smillier/BeerTapRoundDisplay/Case/image.JPG

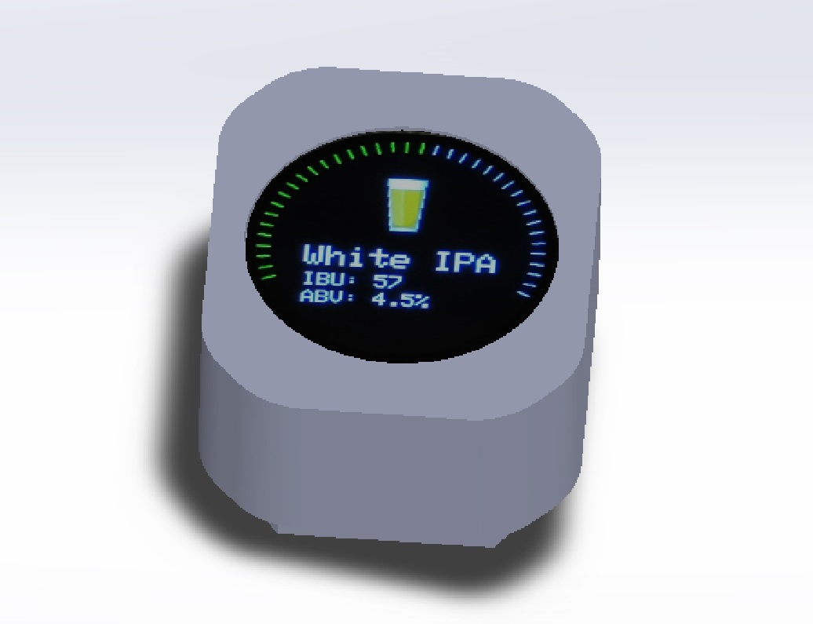
Case/image.JPG
