smillier/BeerTapRoundDisplay/doc/IMG_20211112_064714.jpg

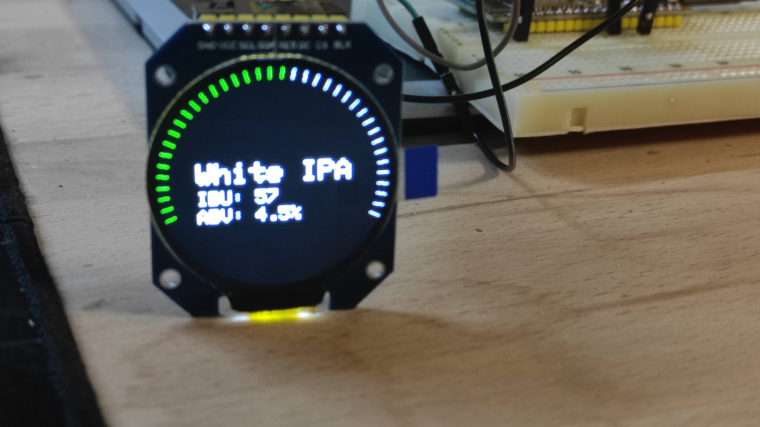
doc/IMG_20211112_064714.jpg
