smillier/BeerTapRoundDisplay/doc/IMG_20220213_194237.jpg

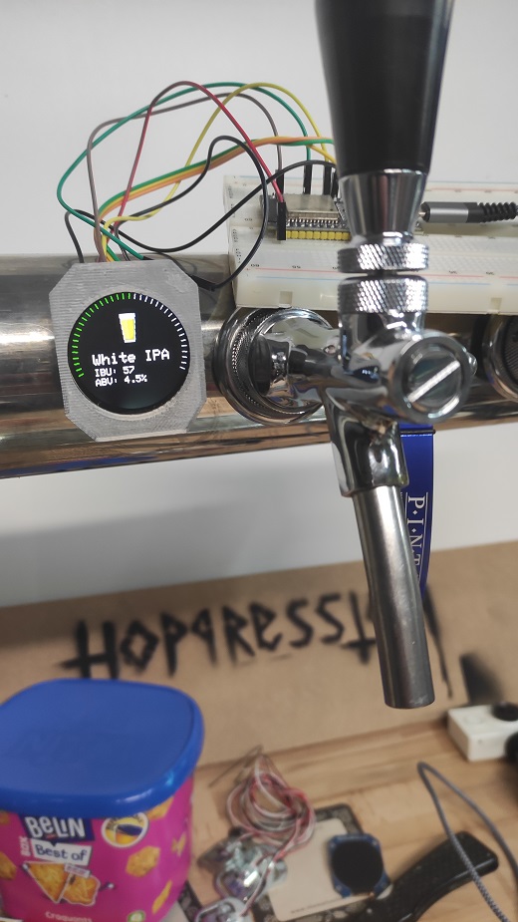
doc/IMG_20220213_194237.jpg
