smillier/BeerTapRoundDisplay/doc/IMG_20220216_224940.jpg

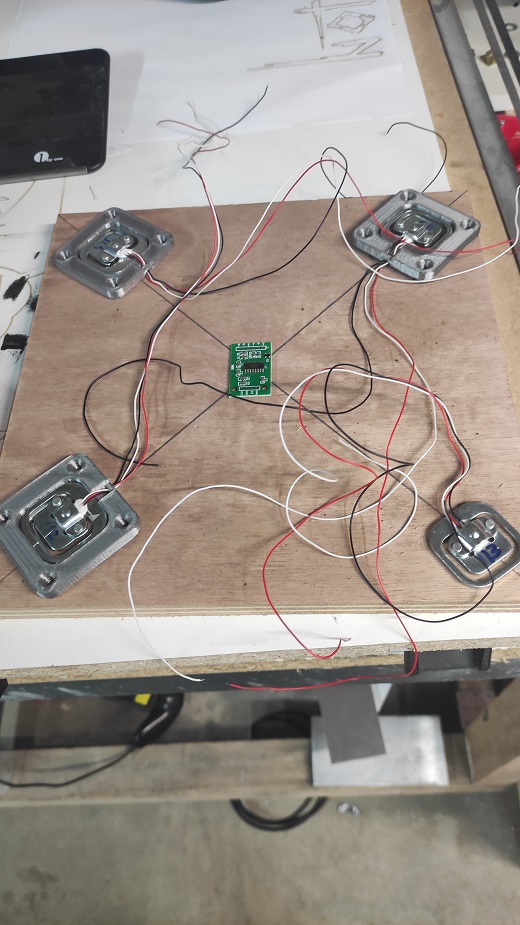
doc/IMG_20220216_224940.jpg
