smillier/BeerTapRoundDisplay/doc/IMG_20220629_192002.jpg

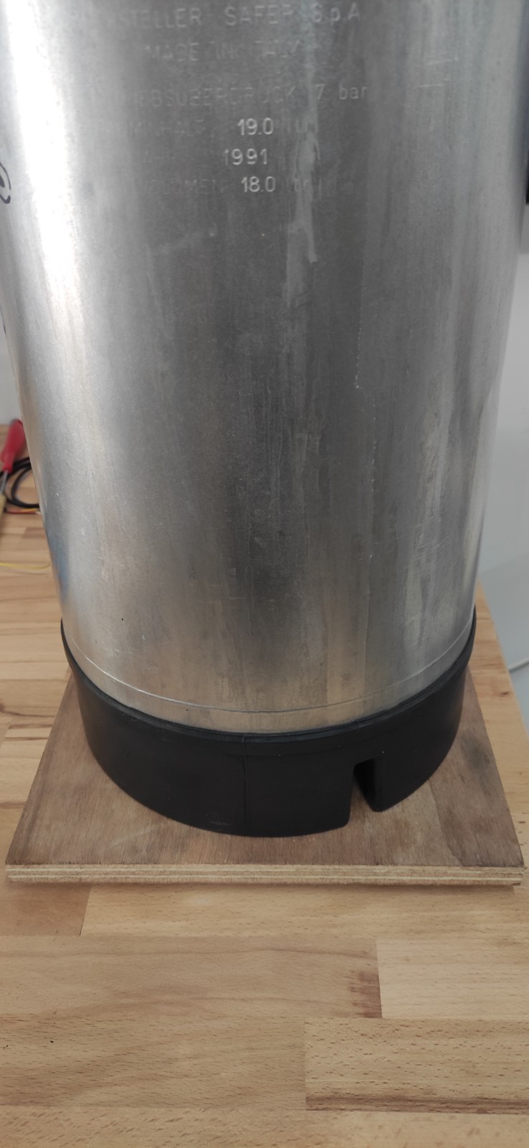
doc/IMG_20220629_192002.jpg
