smillier/BeerTapRoundDisplay/doc/IMG_20220629_192141.jpg

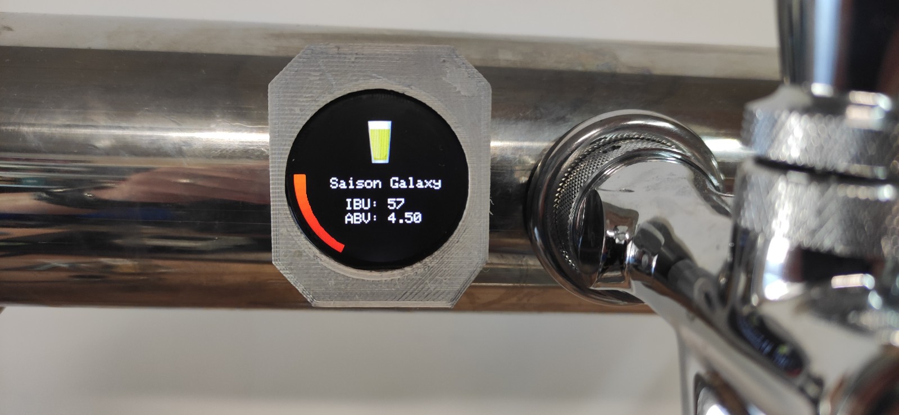
doc/IMG_20220629_192141.jpg
