smillier/BeerTapRoundDisplay/doc/ModuleDimensions.JPG

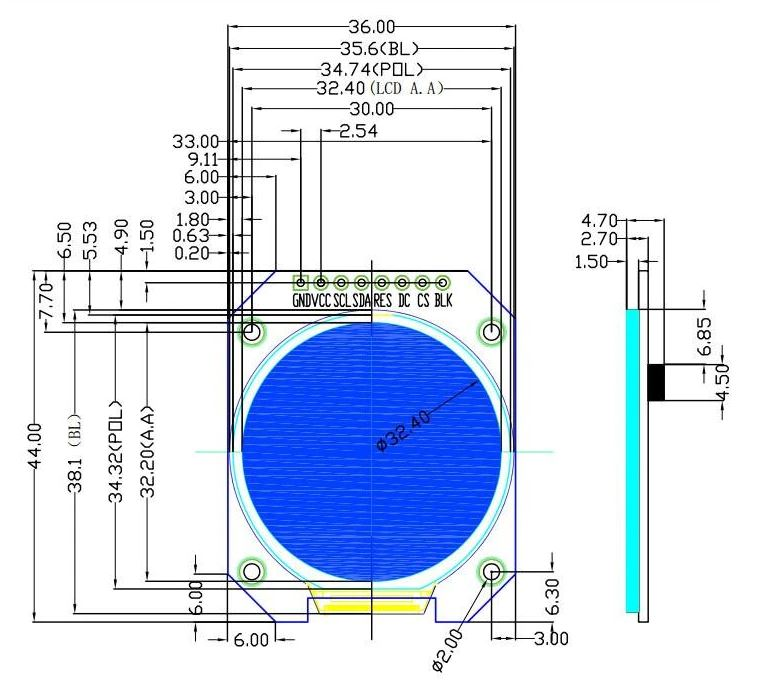
doc/ModuleDimensions.JPG
