smillier/BeerTapRoundDisplay/doc/NSRM12.png

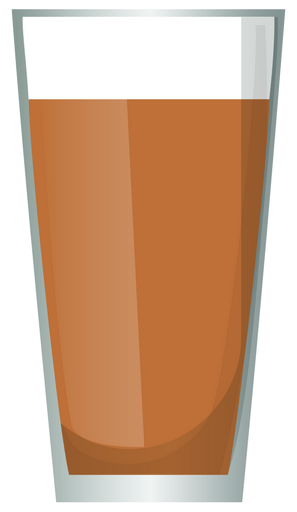
doc/NSRM12.png
