smillier/BeerTapRoundDisplay/src/setup.cpp

#include "setup.h"
#include "FS.h"
#include <SPIFFS.h>
#include <WiFi.h>

#include <AsyncTCP.h>
#include <ESPAsyncWebServer.h>
#include <AsyncElegantOTA.h>
#define _ESPASYNC_WIFIMGR_LOGLEVEL_    3
#include <WiFiClient.h>
#include <ESPmDNS.h>
#include <ArduinoOTA.h>
#include <ESPAsync_WiFiManager.h> 
#include "weightmeasure.h"
#include "display.h"
AsyncWebServer server(80);
#include "config.h"
#include "Preferences.h"

//Preferences preference;

void initialize()
{
  Serial.println("Init display");

  
 //AsyncWebServer webServer(80);
#if !( USING_ESP32_S2 || USING_ESP32_C3 )
DNSServer dnsServer;
#endif
//const char *ssid = "";
//const char *password = "";

  Serial.begin(115200);
  Serial.println("\n");
  Serial.println("Connexion etablie!");
  Serial.print("Adresse IP: ");
  Serial.println(WiFi.localIP());
  //mDNS Responder
  // Set up mDNS responder:
    // - first argument is the domain name, in this example
    //   the fully-qualified domain name is "esp32.local"
    // - second argument is the IP address to advertise
    //   we send our IP address on the WiFi network
    if (!MDNS.begin("BeerTapDisplay.local")) {
        Serial.println("Error setting up MDNS responder!");
        while(1) {
            delay(1000);
        }
    }
    Serial.println("mDNS responder started");

    Serial.println("TCP server started");

    // Add service to MDNS-SD
    MDNS.addService("http", "tcp", 80);
    //----------------------------------------------------OTA
  Serial.println("Starting OTA...");
  
    #if ( USING_ESP32_S2 || USING_ESP32_C3 )
  ESPAsync_WiFiManager ESPAsync_wifiManager(&server, NULL, "Bottle_Filler_Autoconnect");
#else
  ESPAsync_WiFiManager ESPAsync_wifiManager(&server, &dnsServer, "TapDisplay");
#endif  
  //ESPAsync_wifiManager.resetSettings();   //reset saved settings
  ESPAsync_wifiManager.setAPStaticIPConfig(IPAddress(192,168,4,1), IPAddress(192,168,4,1), IPAddress(255,255,255,0));
  ESPAsync_wifiManager.autoConnect("TapDisplay_AP");
  if (WiFi.status() == WL_CONNECTED) { Serial.print(F("Connected. Local IP: ")); Serial.println(WiFi.localIP()); }
  else { Serial.println(ESPAsync_wifiManager.getStatus(WiFi.status())); }
 
 ArduinoOTA
    .onStart([]() {
      String type;
      if (ArduinoOTA.getCommand() == U_FLASH)
        type = "sketch";
      else // U_SPIFFS
        type = "filesystem";

      // NOTE: if updating SPIFFS this would be the place to unmount SPIFFS using SPIFFS.end()
      Serial.println("Start updating " + type);
    })
    .onEnd([]() {
      Serial.println("\nEnd");
    })
    .onProgress([](unsigned int progress, unsigned int total) {
      Serial.printf("Progress: %u%%\r", (progress / (total / 100)));
    })
    .onError([](ota_error_t error) {
      Serial.printf("Error[%u]: ", error);
      if (error == OTA_AUTH_ERROR) Serial.println("Auth Failed");
      else if (error == OTA_BEGIN_ERROR) Serial.println("Begin Failed");
      else if (error == OTA_CONNECT_ERROR) Serial.println("Connect Failed");
      else if (error == OTA_RECEIVE_ERROR) Serial.println("Receive Failed");
      else if (error == OTA_END_ERROR) Serial.println("End Failed");
    });
    
    ArduinoOTA.begin();

    AsyncElegantOTA.begin(&server);    // Start ElegantOTA
  server.begin();
  Serial.println("Serveur actif!");
  
  if(!SPIFFS.begin()){
        Serial.println("SPIFFS Mount Failed");
        return;
    }
     
     display_init();
   Serial.println("Scale setup");
 scale_setup();
  //scale_calibrate();
 
}


void initWebServer()
{
   //----------------------------------------------------SERVER
  server.on("/", HTTP_GET, [](AsyncWebServerRequest *request)
            { request->send(SPIFFS, "/index.html", "text/html"); });

  server.on("/w3.css", HTTP_GET, [](AsyncWebServerRequest *request)
            { request->send(SPIFFS, "/w3.css", "text/css"); });

  server.on("/script.js", HTTP_GET, [](AsyncWebServerRequest *request)
            { request->send(SPIFFS, "/script.js", "text/javascript"); });

  server.on("/jquery-3.4.1.min.js", HTTP_GET, [](AsyncWebServerRequest *request)
            { request->send(SPIFFS, "/jquery-3.4.1.min.js", "text/javascript"); });

  server.on("/param.xml", HTTP_GET, [](AsyncWebServerRequest *request)
            { 
              request->send(SPIFFS, "/param.xml", "text/xml");});

  server.on("/wparamxml", HTTP_POST, [](AsyncWebServerRequest *request)
            { 
                Serial.println("wparam");
                File file = SPIFFS.open("/param.xml","w");
                String message;
                message = request->getParam("wparamxml", true)->value();
                Serial.println(message);
                file.print(message);

              request->send(204);});

  server.on("/weight", HTTP_GET, [](AsyncWebServerRequest *request)
            {
              float sensorValue = getWeight();
              //int val = analogRead(capteurPression);
              String Value = String(sensorValue);
              request->send(200, "text/plain", Value);
              Serial.println(Value);
            });
  server.on("/on", HTTP_GET, [](AsyncWebServerRequest *request)
            {
              //etatLedVoulu = 1;
              request->send(204);
             // Serial.println("On");
            });

  server.on("/off", HTTP_GET, [](AsyncWebServerRequest *request)
            {
              //etatLedVoulu = 0;
              //digitalWrite(led, LOW);
              //etatLed = 0;
              request->send(204);
              // Serial.println("off");
            });

  server.on("/delayLed", HTTP_POST, [](AsyncWebServerRequest *request)
            {
              if (request->hasParam("valeurDelayLed", true))
              {
                String message;
                message = request->getParam("valeurDelayLed", true)->value();
                //if(message.toInt()!=0)
                //valeurDelayLed = message.toInt();
                Serial.println("valeurDelayLed");
              }
              request->send(204);
            });
  server.on("/beer_name", HTTP_POST, [](AsyncWebServerRequest *request)
            {
              if (request->hasParam("beer_name", true))
              {
                String message;
                message = request->getParam("beer_name", true)->value();
                setBeerName(message);
               // preference.putString("beer_name",message);
                
                 Serial.println("beer_name");
              }
              request->send(204);
            });

    server.on("/beer_ibu", HTTP_POST, [](AsyncWebServerRequest *request)
            {
              if (request->hasParam("beer_ibu", true))
              {
                String message;
                message = request->getParam("beer_ibu", true)->value();
                if(message.toInt()!=0)
                setBeerIBU(message.toInt());
                Serial.println("beer_ibu");
              }
              int ibu = getBeerIBU();
              String Value = String(ibu);
                Serial.println(Value);
              request->send(200, "text/plain", Value);
              //request->send(204);
            });
   server.on("/beer_ebc", HTTP_POST, [](AsyncWebServerRequest *request)
            {
              int EBC = getBeerEBC();
              if (request->hasParam("beer_ebc", true))
              {
                String message;
                message = request->getParam("beer_ebc", true)->value();
                if(message.toInt()!=0)
                  setBeerEBC(message.toInt());
                //valeurDelayLed = message.toInt();
                Serial.println("beer_ebc");
              }
              
               Serial.println((String)EBC);
              request->send(200, "text/plain", (String)EBC);
             
            });
   server.on("/beer_abv", HTTP_POST, [](AsyncWebServerRequest *request)
            {
              float ABV = getBeerABV();
              if (request->hasParam("beer_abv", true))
              {
                String message;
                message = request->getParam("beer_abv", true)->value();
               if(message.toFloat()!=0.0)
                ABV = message.toFloat();
                setBeerABV(ABV);
                Serial.println("beer_abv");
              }
              request->send(200, "text/plain", (String)ABV);
            });
    server.on("/beer_sg", HTTP_POST, [](AsyncWebServerRequest *request)
            {
              float sg = getBeerSg();
              if (request->hasParam("beer_sg", true))
              {
                String message;
                message = request->getParam("beer_sg", true)->value();
               if(message.toFloat()!=0.0)
                sg = message.toFloat();
                setBeerSg(sg);
                Serial.println("beer_sg");
              }
              request->send(200, "text/plain", (String)sg);
            });
           // preference.end();
}
